Golowa70/CAR-BS-CONTROLLER-NEX/Photo/20210625_010253.jpg

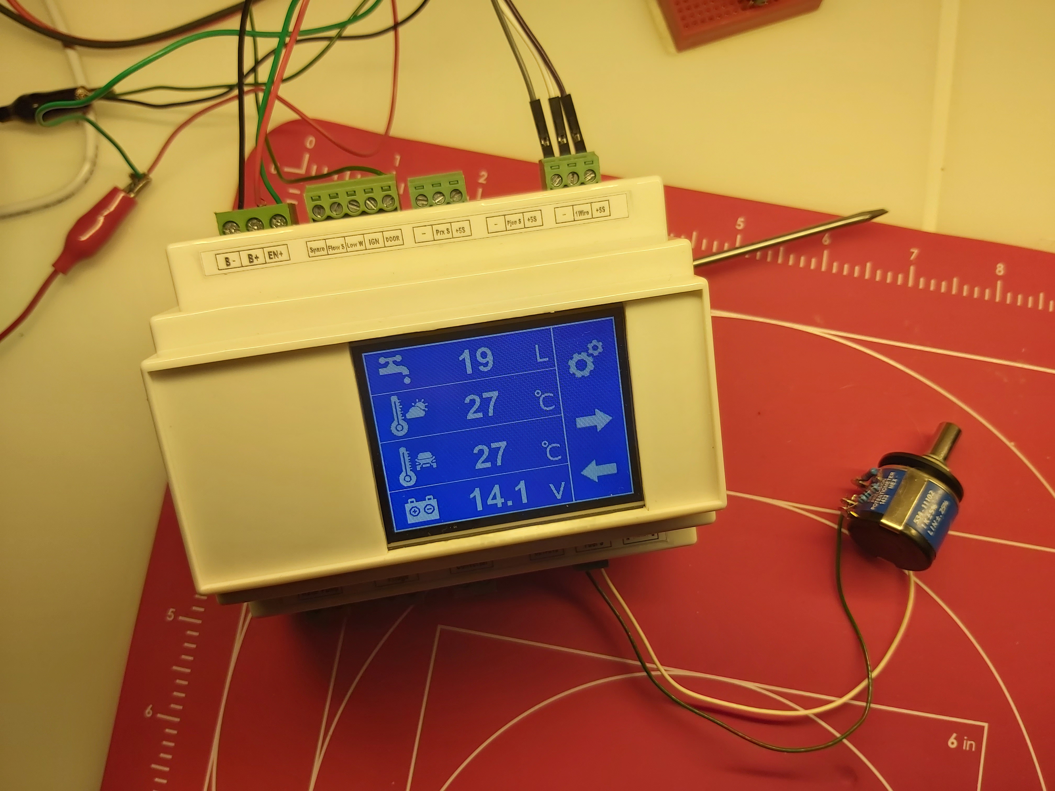
Photo/20210625_010253.jpg
