Golowa70/CAR-BS-CONTROLLER-NEX/Photo/20210704_170350.jpg

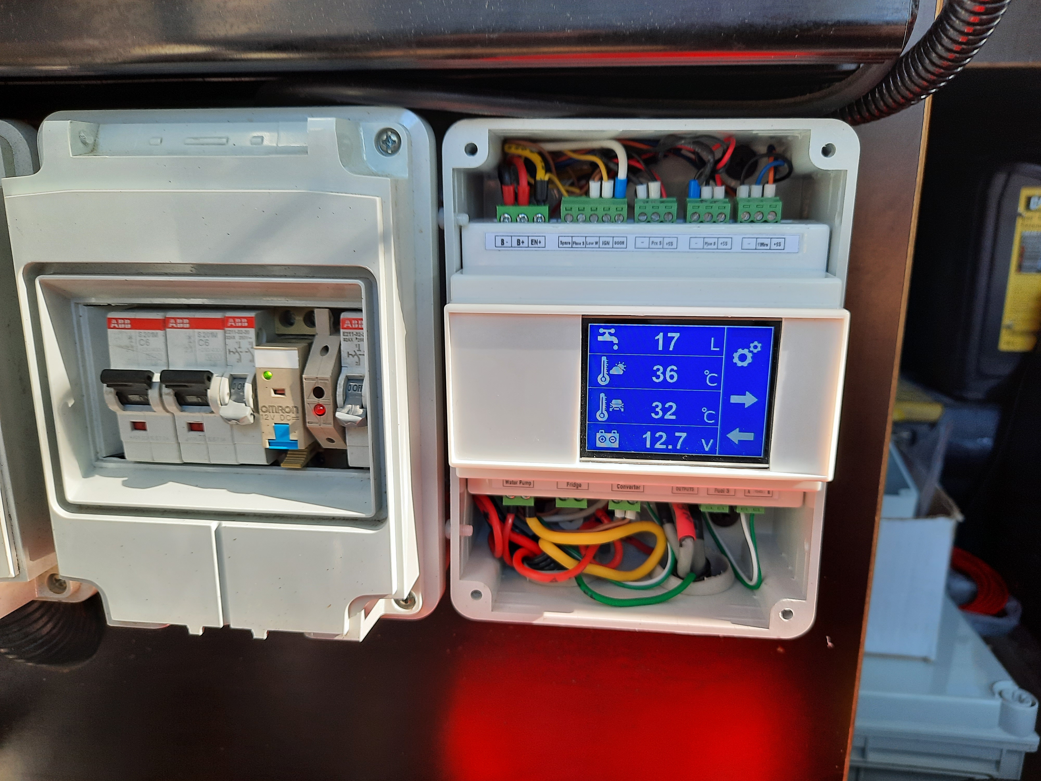
Photo/20210704_170350.jpg
