Golowa70/CAR-BS-CONTROLLER-NEX/Photo/IMG_20210617_063625.jpg

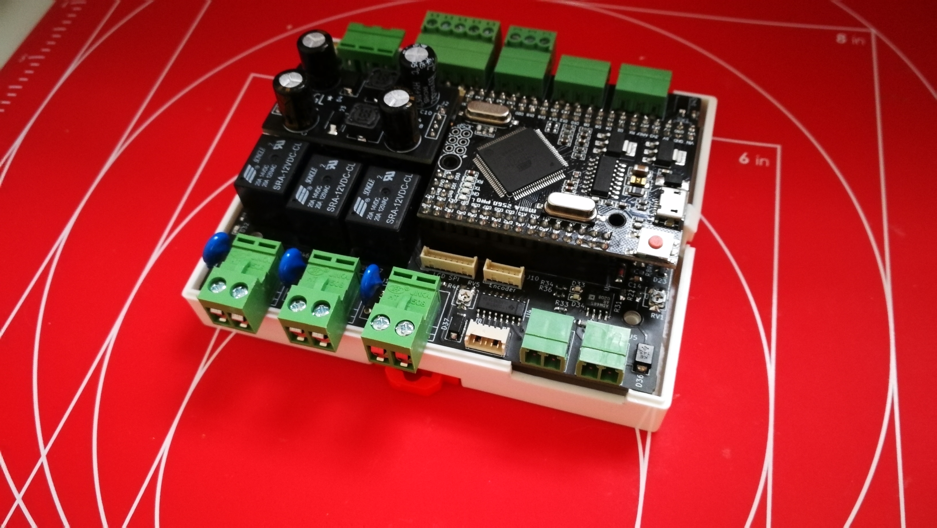
Photo/IMG_20210617_063625.jpg
