Golowa70/CAR-BS-CONTROLLER-NEX/Photo/IMG_20210619_175207.jpg

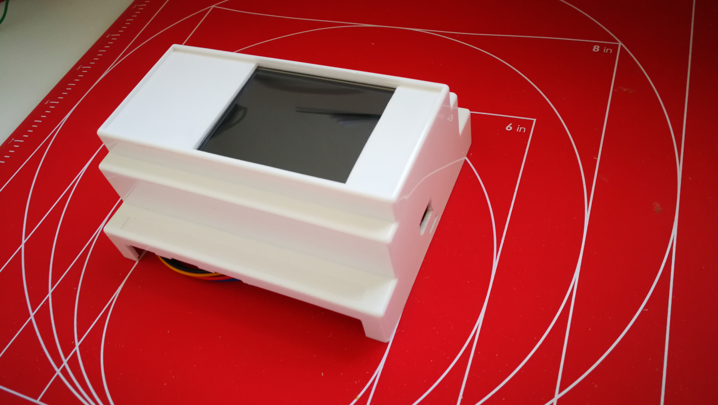
Photo/IMG_20210619_175207.jpg
