Golowa70/CAR-BS-CONTROLLER-NEX/Photo/IMG_20210619_175216.jpg

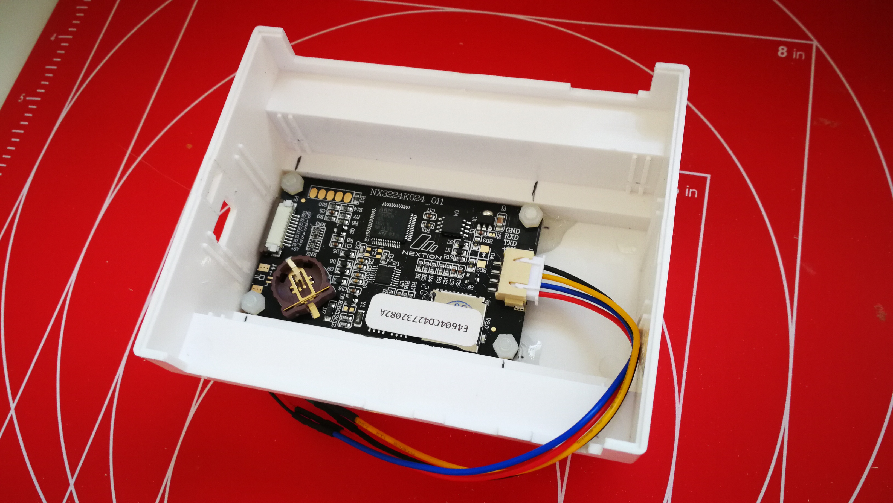
Photo/IMG_20210619_175216.jpg
