Golowa70/CAR-BS-CONTROLLER-NEX/Photo/IMG_20210619_180213.jpg

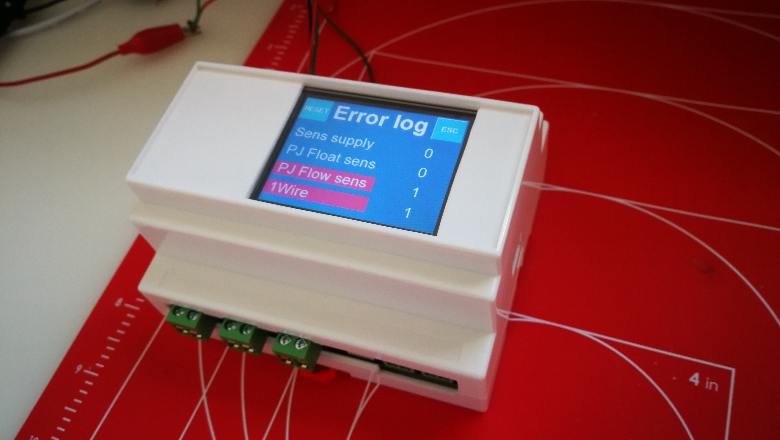
Photo/IMG_20210619_180213.jpg
